Ghost-af16/Core-65/Cart screenshot/Screenshot 2025-12-07 122132.png

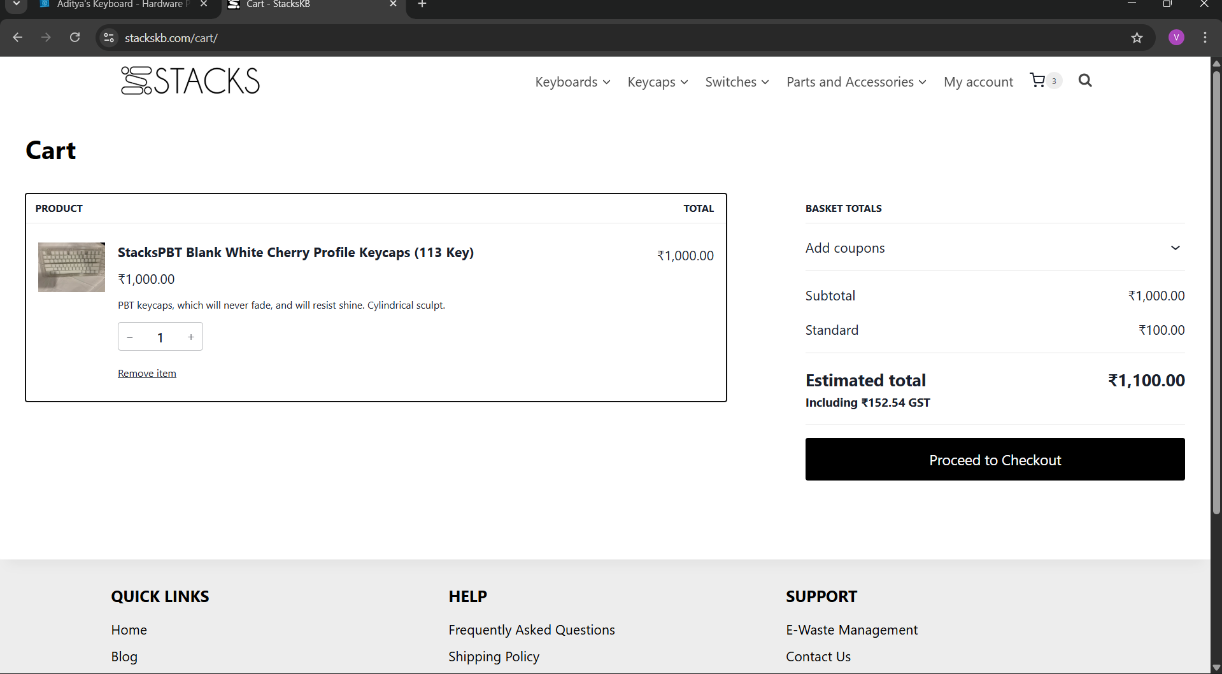
Cart screenshot/Screenshot 2025-12-07 122132.png
