Ghost-af16/Core-65/Cart screenshot/Screenshot 2025-12-19 232334.png

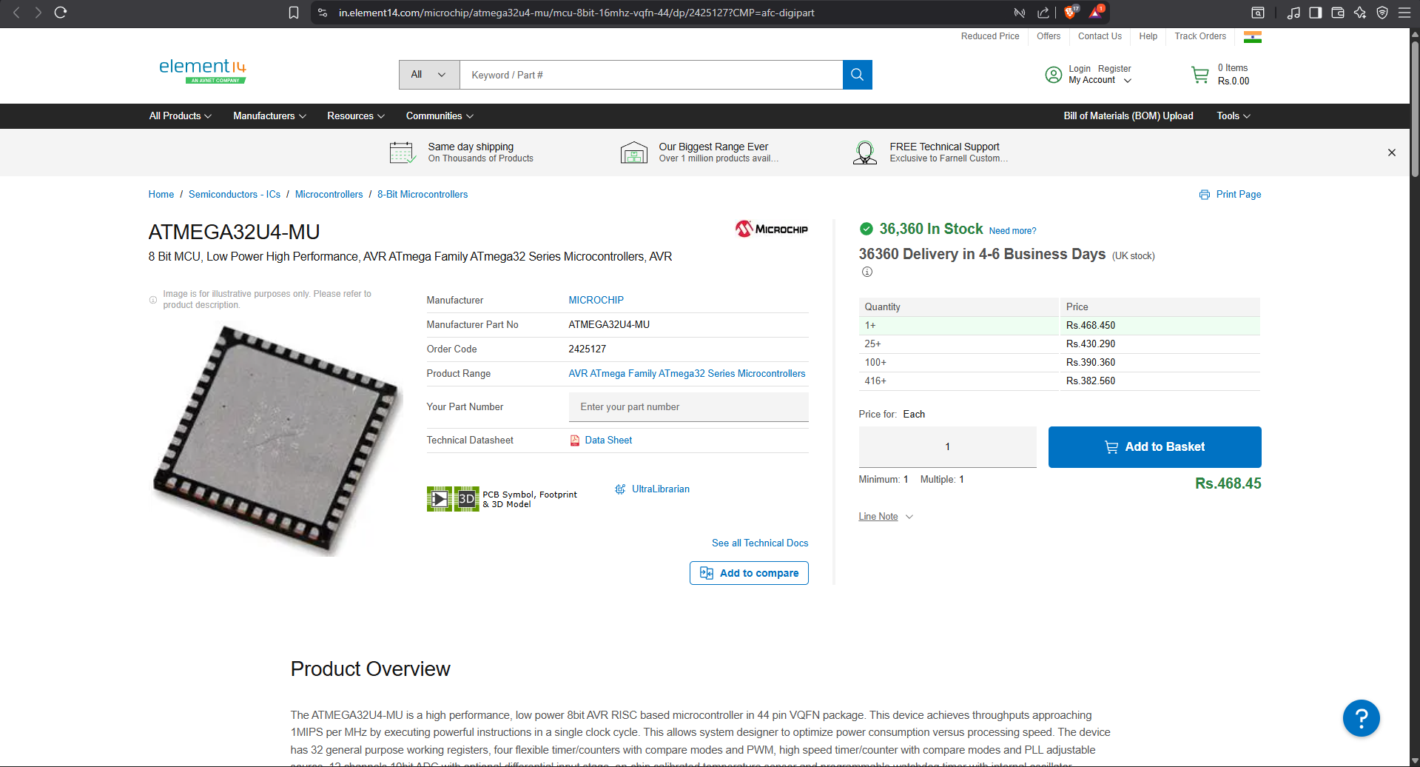
Cart screenshot/Screenshot 2025-12-19 232334.png
