Ghost-af16/Core-65/Cart screenshot/Screenshot 2025-12-19 233557.png

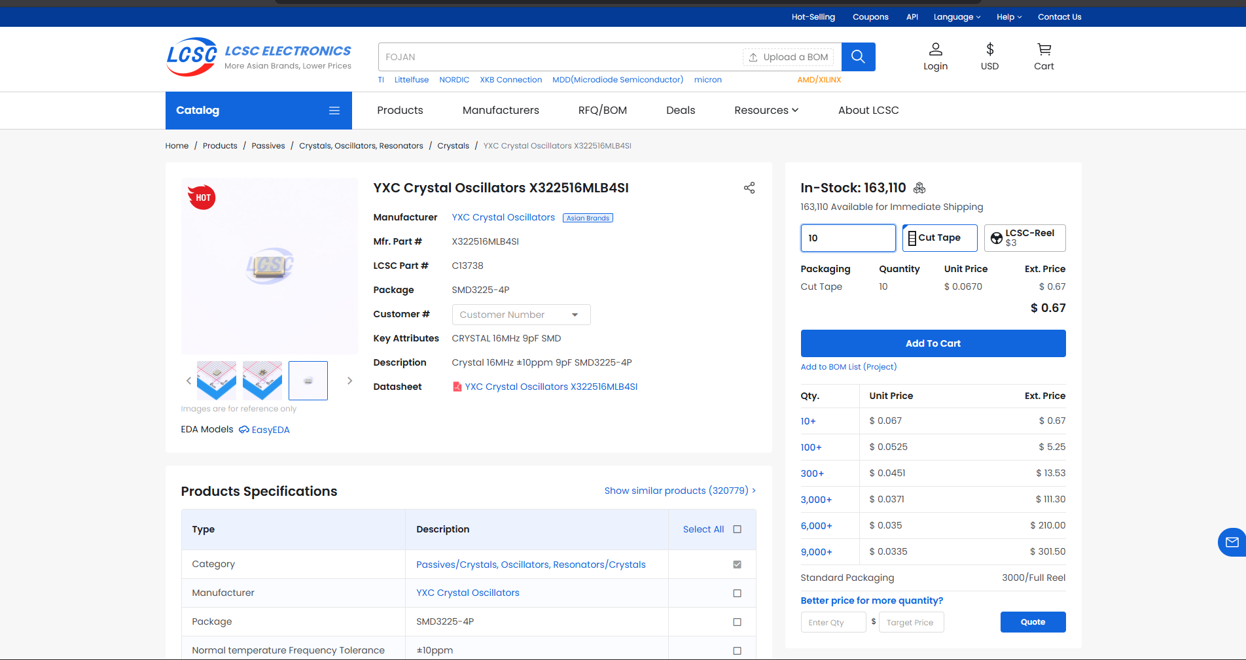
Cart screenshot/Screenshot 2025-12-19 233557.png
