Ghost-af16/Core-65/Cart screenshot/Screenshot 2025-12-20 000902.png

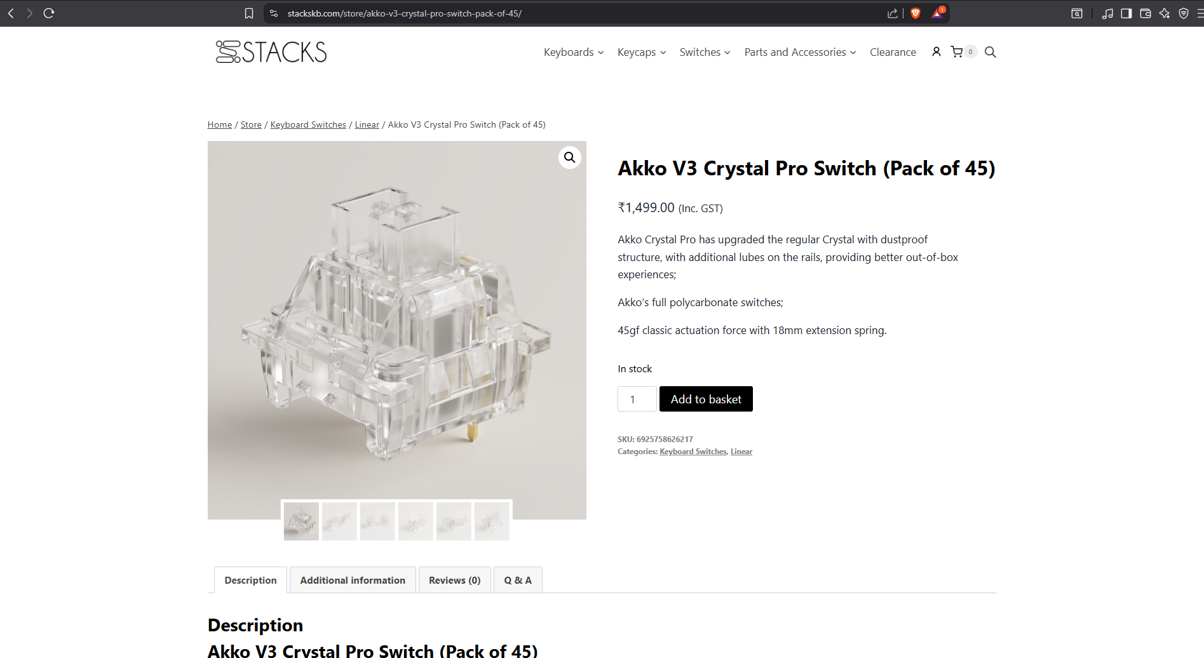
Cart screenshot/Screenshot 2025-12-20 000902.png
