Ghost-af16/Core-65/Cart screenshot/Screenshot 2025-12-24 125706.png

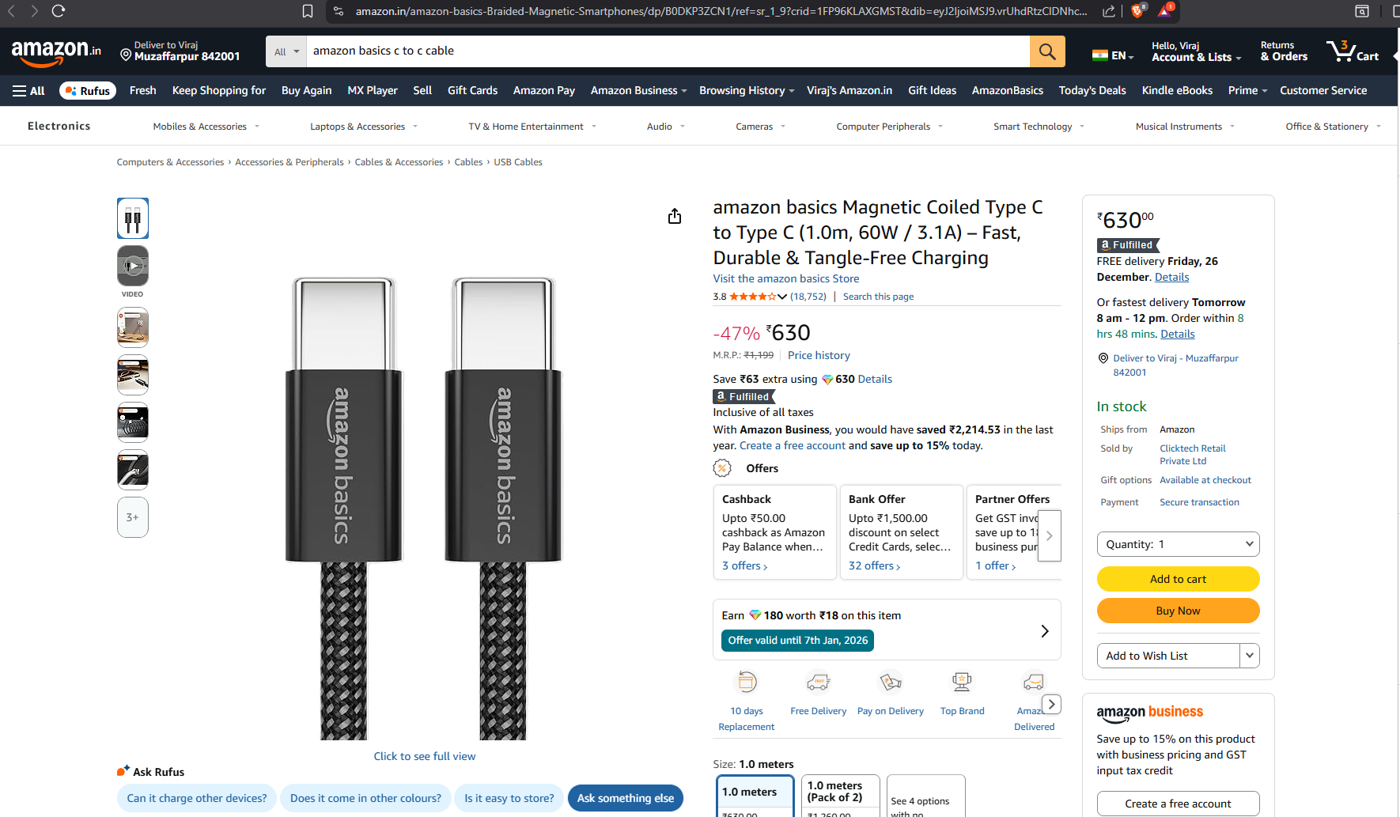
Cart screenshot/Screenshot 2025-12-24 125706.png
