Ghost-af16/Core-65/Cart screenshot/Screenshot 2026-01-06 135911.png

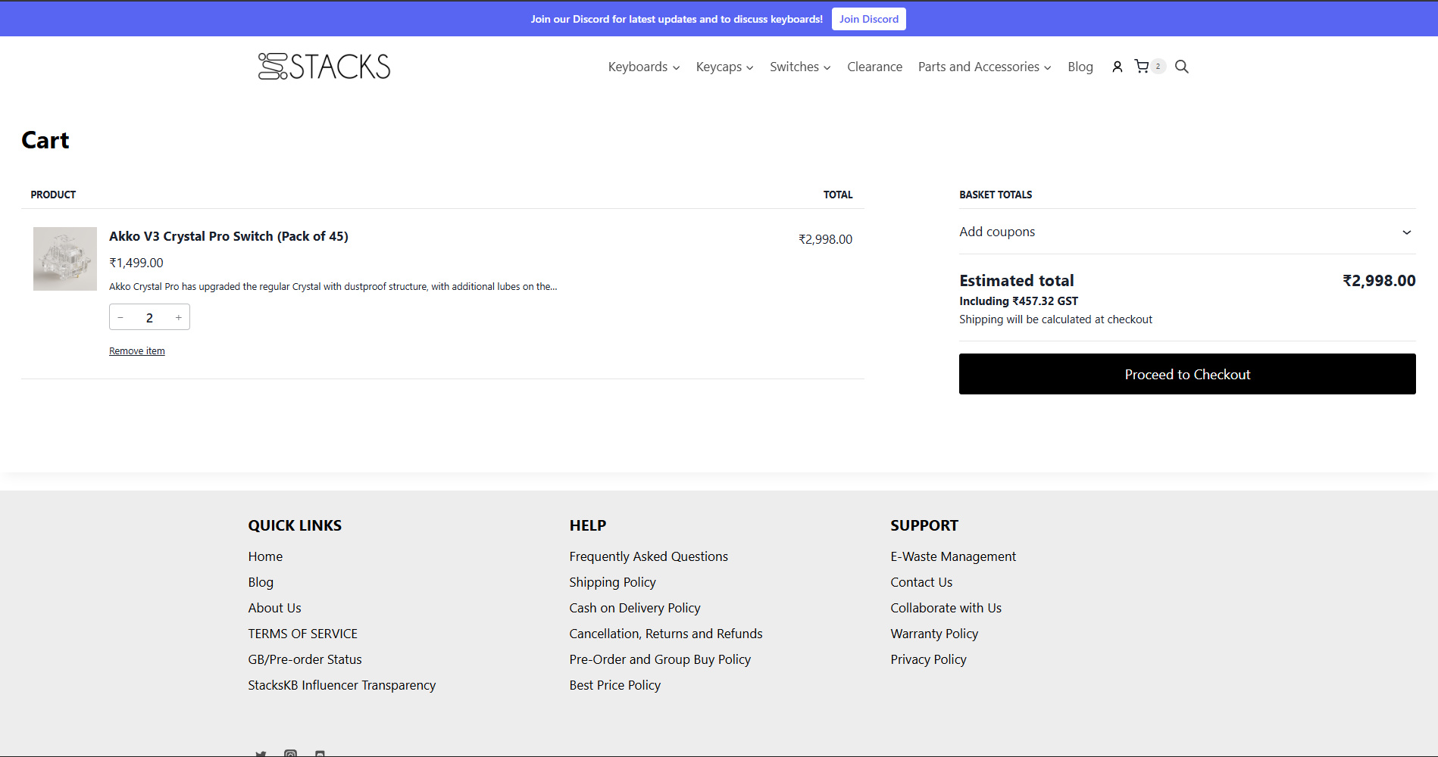
Cart screenshot/Screenshot 2026-01-06 135911.png
