Ghost-af16/Core-65/Cart screenshot/Screenshot 2026-01-06 140223.png

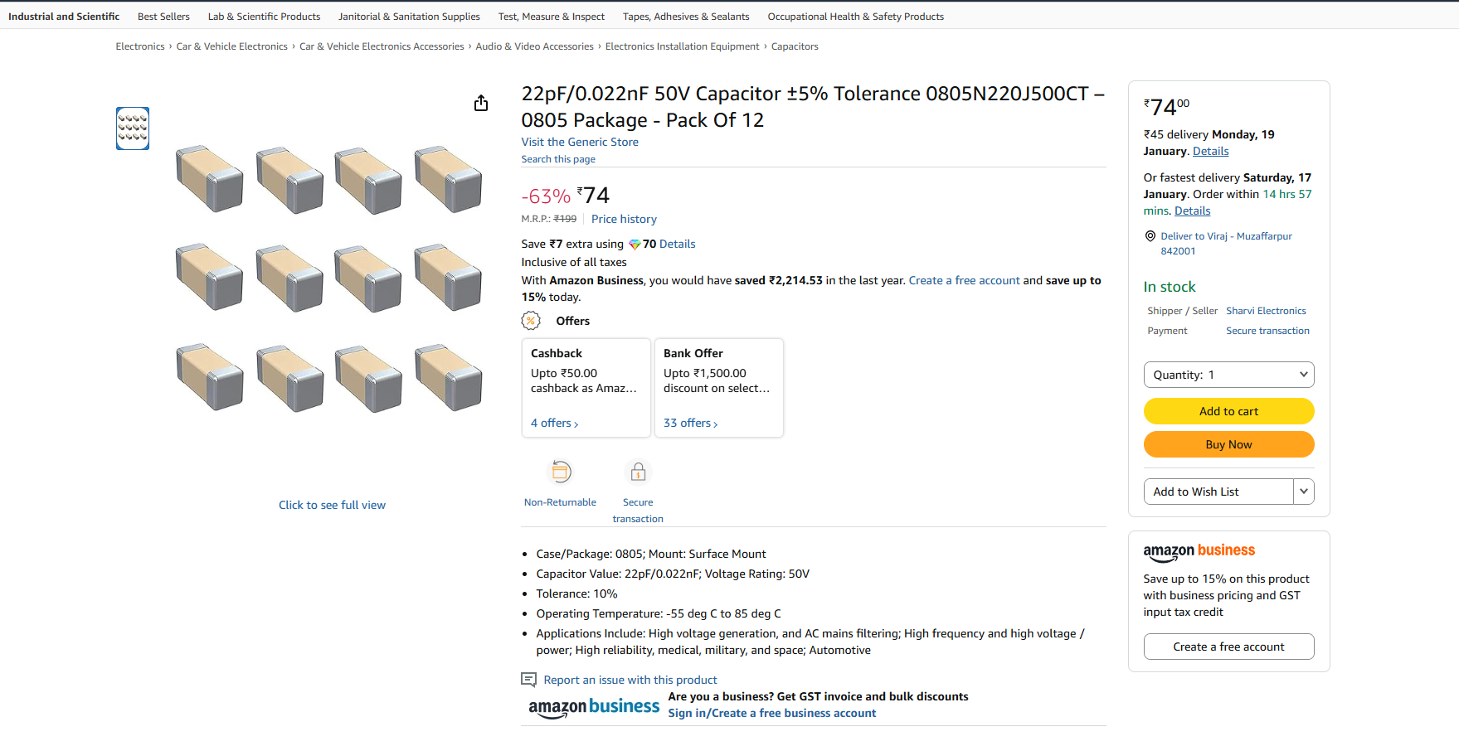
Cart screenshot/Screenshot 2026-01-06 140223.png
