Ghost-af16/Core-65/Cart screenshot/Screenshot_2026-01-07-13-42-52-47_40deb401b9ffe8e1df2f1cc5ba480b12.jpg

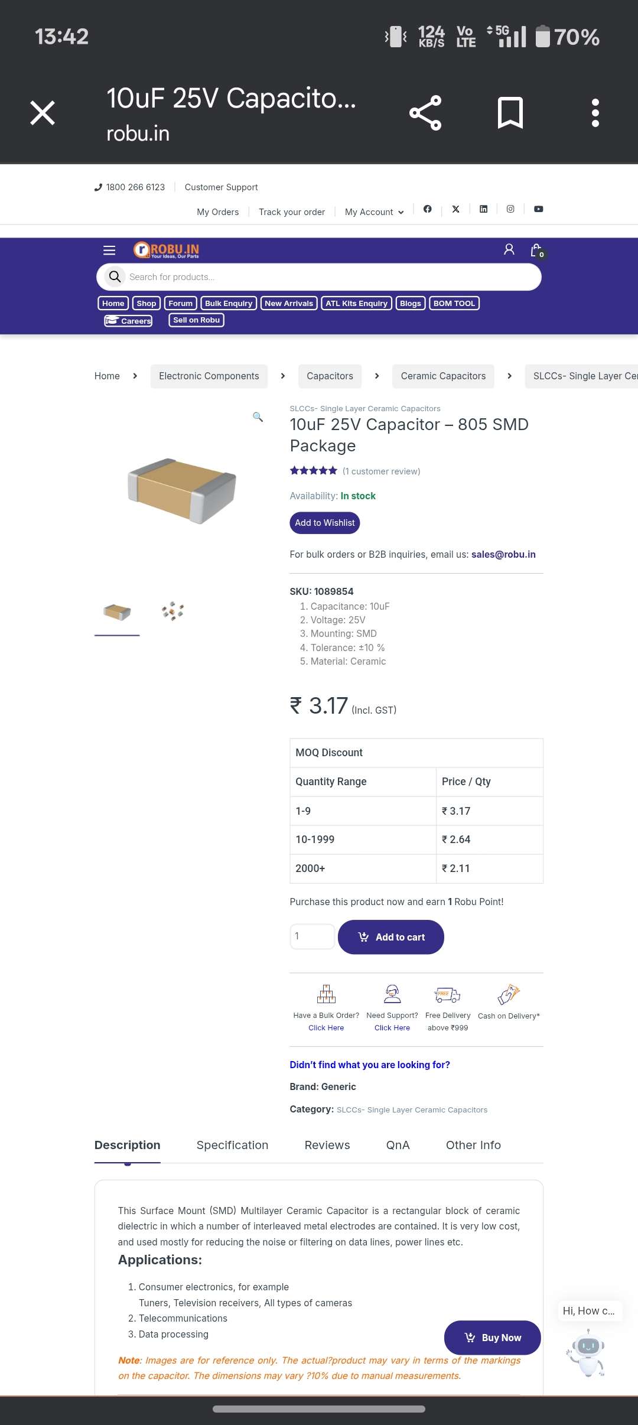
Cart screenshot/Screenshot_2026-01-07-13-42-52-47_40deb401b9ffe8e1df2f1cc5ba480b12.jpg
